shop2007/Camper_energy_saver/bluetooth_HC06/hc05-modulo.png

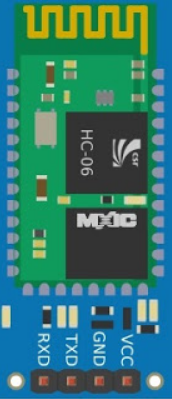
bluetooth_HC06/hc05-modulo.png
