shop2007/Camper_energy_saver/bluetooth_HC06/HC05.jpg

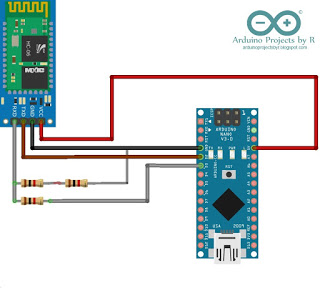
bluetooth_HC06/HC05.jpg
