shop2007/Camper_energy_saver/PDF-immagini/Apparato aperto.jpg

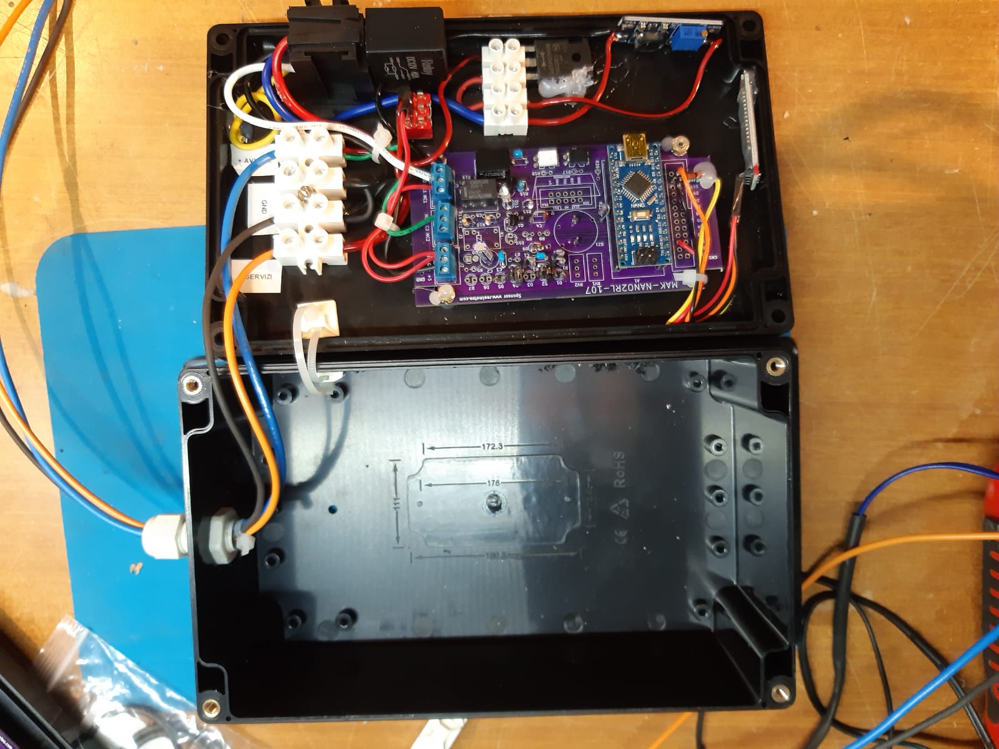
PDF-immagini/Apparato aperto.jpg
