shop2007/Camper_energy_saver/PDF-immagini/bluetooth terminal android 1a.jpg

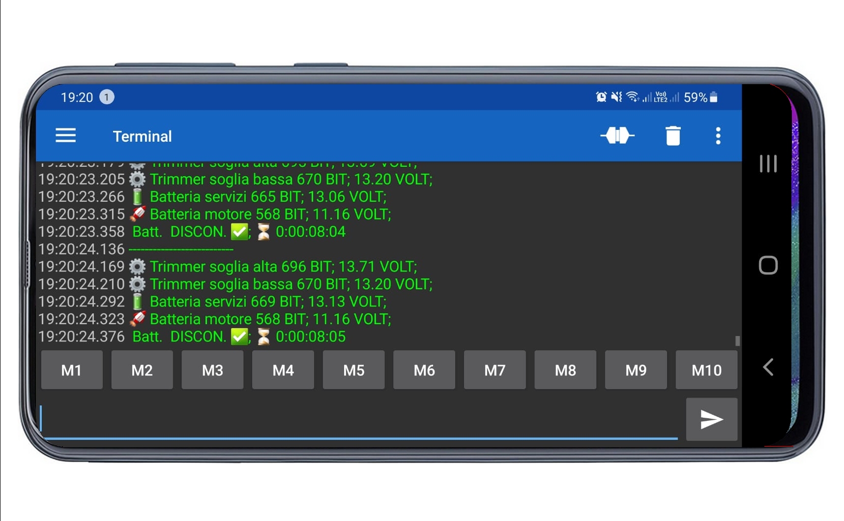
PDF-immagini/bluetooth terminal android 1a.jpg
