shop2007/Camper_energy_saver/PDF-immagini/bluetooth terminal android 2.jpg

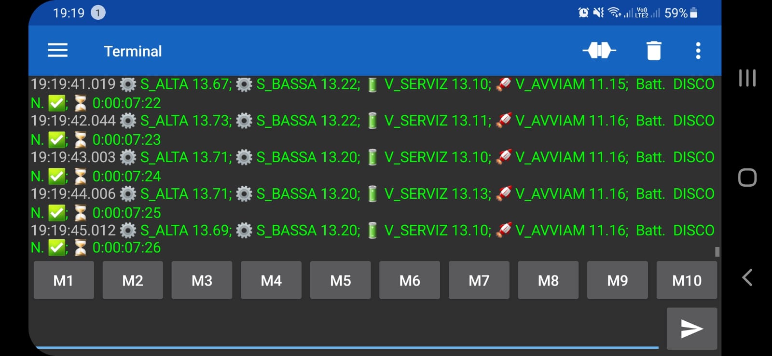
PDF-immagini/bluetooth terminal android 2.jpg
