shop2007/Camper_energy_saver/PDF-immagini/Cablaggio completo.jpg

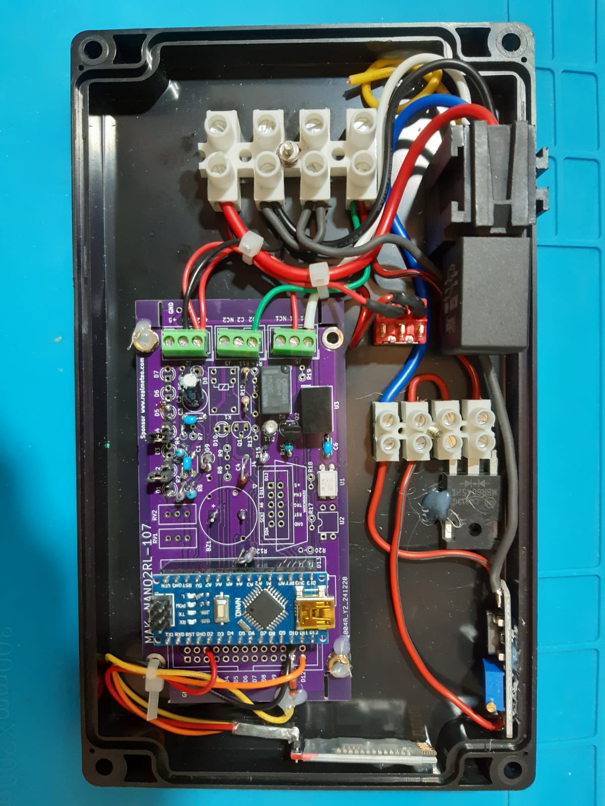
PDF-immagini/Cablaggio completo.jpg
