shop2007/Camper_energy_saver/PDF-immagini/CONNESSIONI.jpg

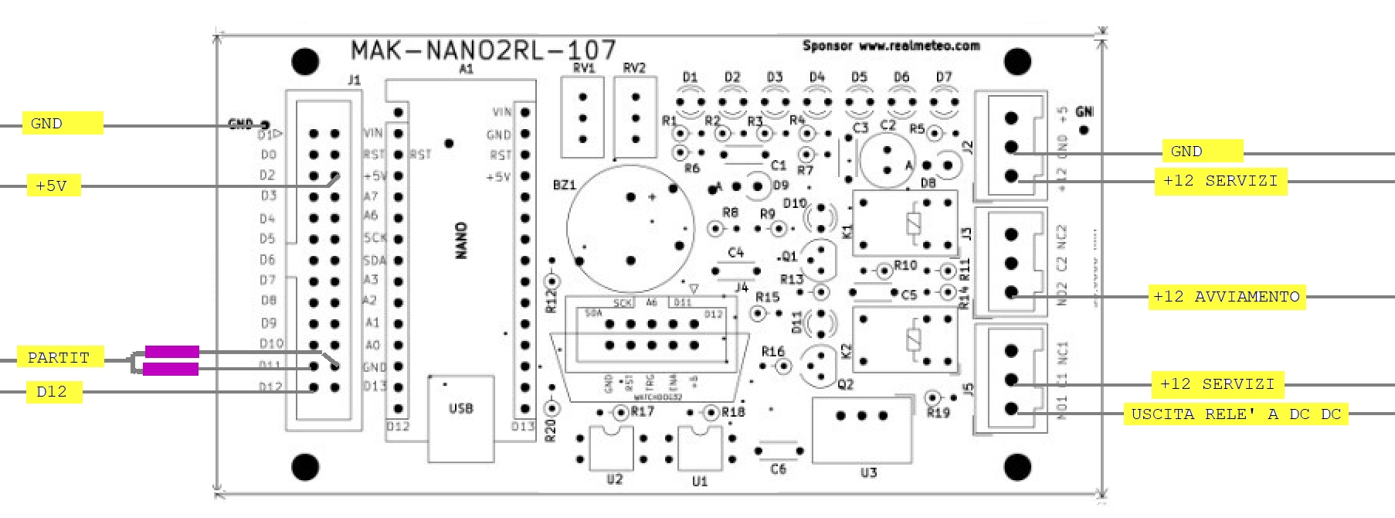
PDF-immagini/CONNESSIONI.jpg
