shop2007/Camper_energy_saver/PDF-immagini/Dettaglio arrivo batterie.jpg

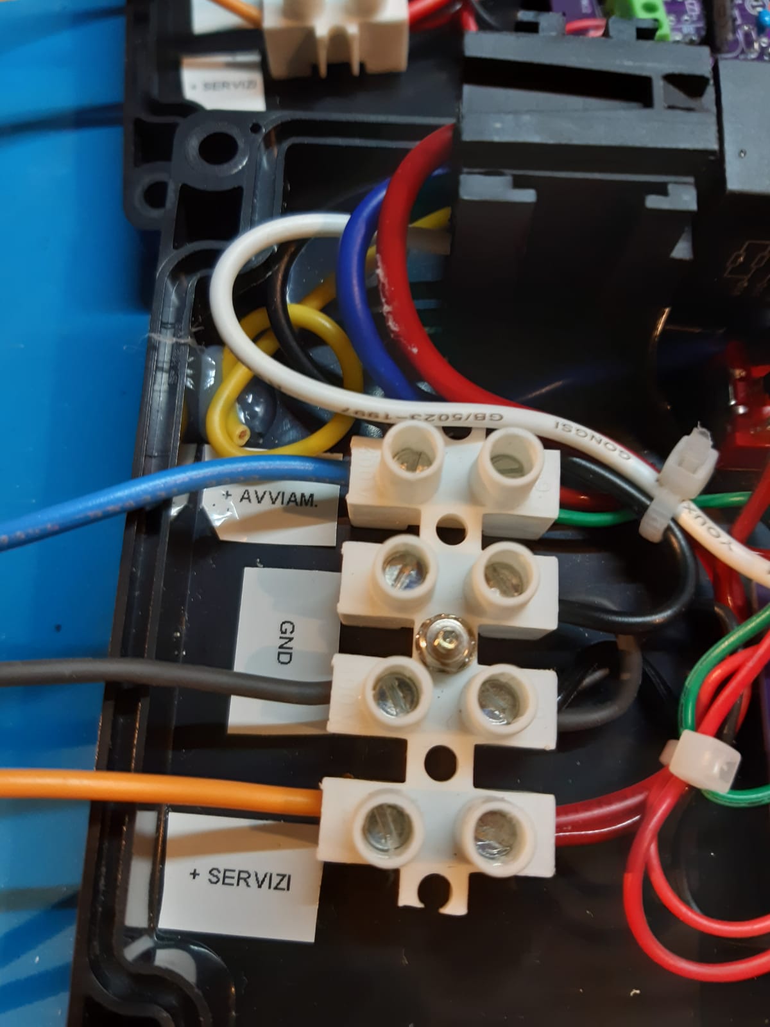
PDF-immagini/Dettaglio arrivo batterie.jpg
