shop2007/Camper_energy_saver/PDF-immagini/Dettaglio cablaggio.jpg

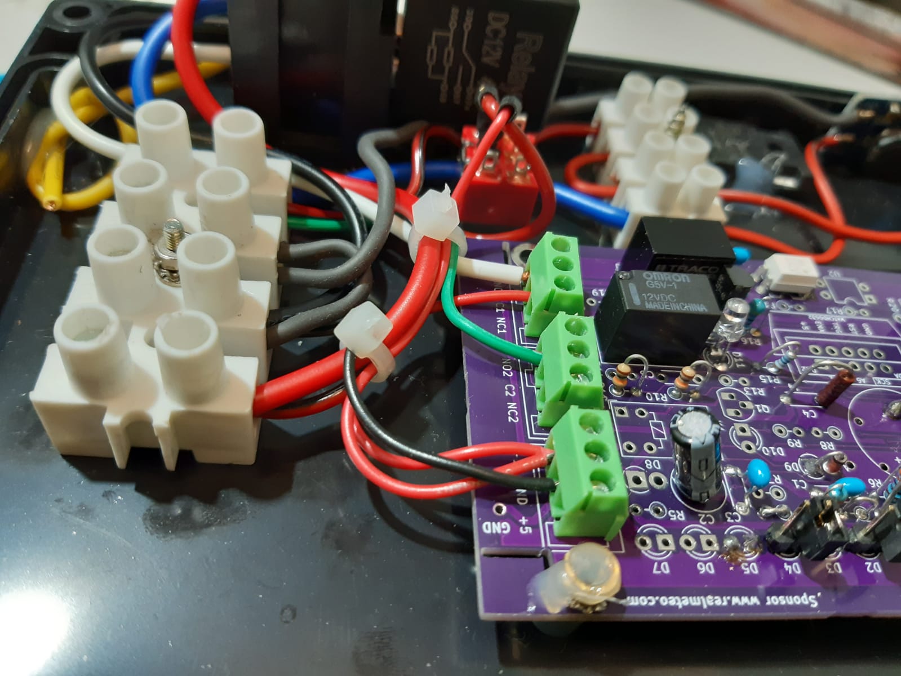
PDF-immagini/Dettaglio cablaggio.jpg
