shop2007/Camper_energy_saver/PDF-immagini/Dettaglio connessione modulo bluetooth.jpg

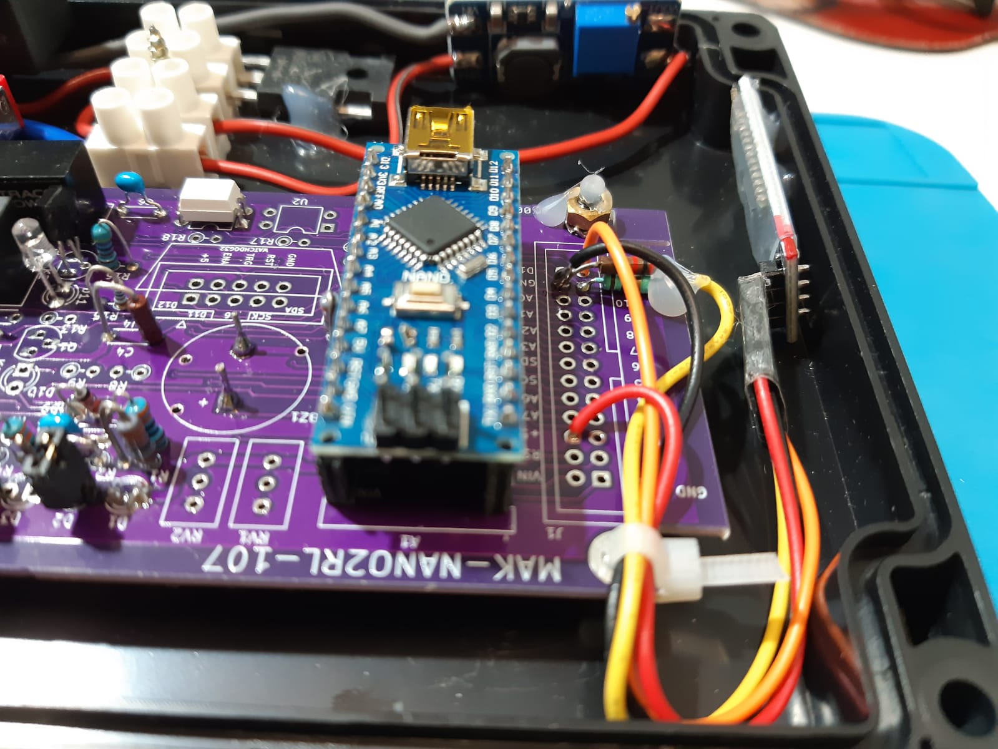
PDF-immagini/Dettaglio connessione modulo bluetooth.jpg
