shop2007/Camper_energy_saver/PDF-immagini/draft-impianto.jpg

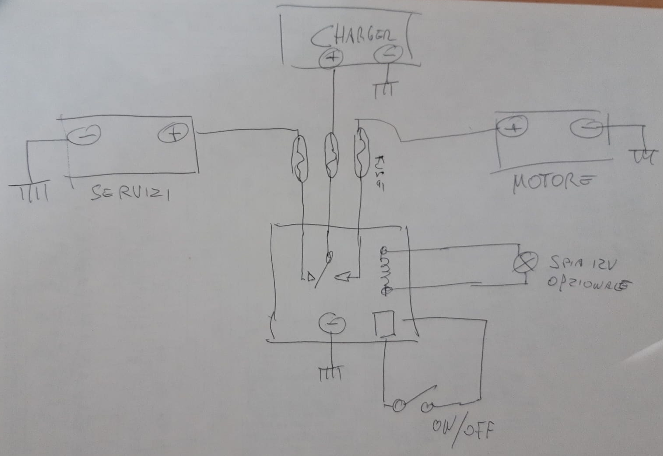
PDF-immagini/draft-impianto.jpg
