shop2007/Camper_energy_saver/PDF-immagini/Due prototipi 2.jpg

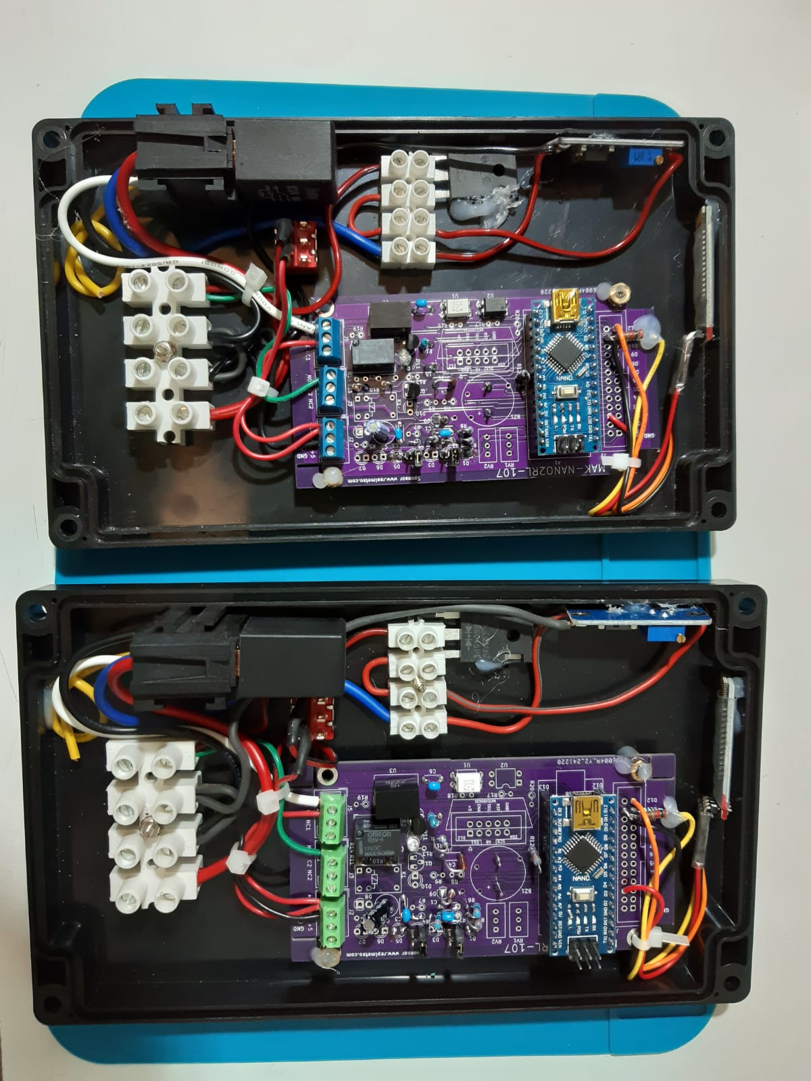
PDF-immagini/Due prototipi 2.jpg
