shop2007/Camper_energy_saver/PDF-immagini/Due prototipi gemelli.jpg

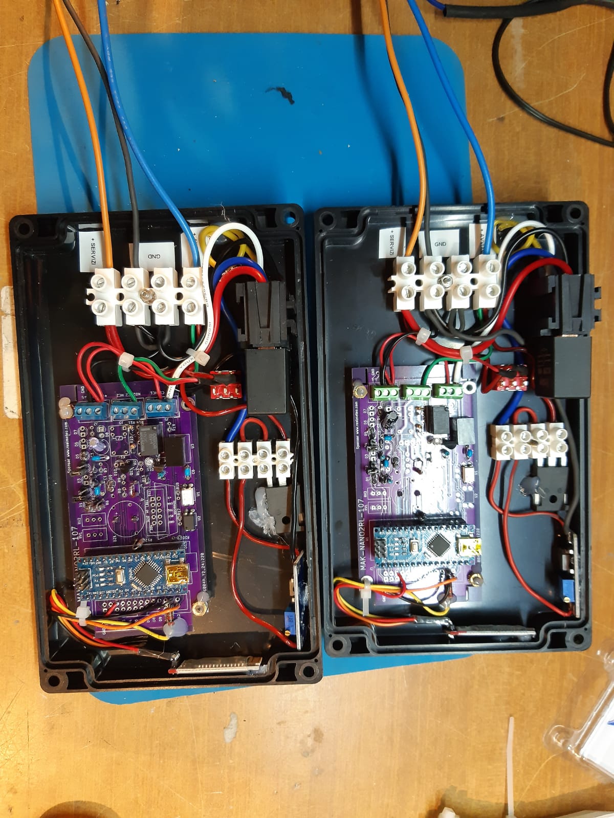
PDF-immagini/Due prototipi gemelli.jpg
