shop2007/Camper_energy_saver/PDF-immagini/led-jumper1.jpg

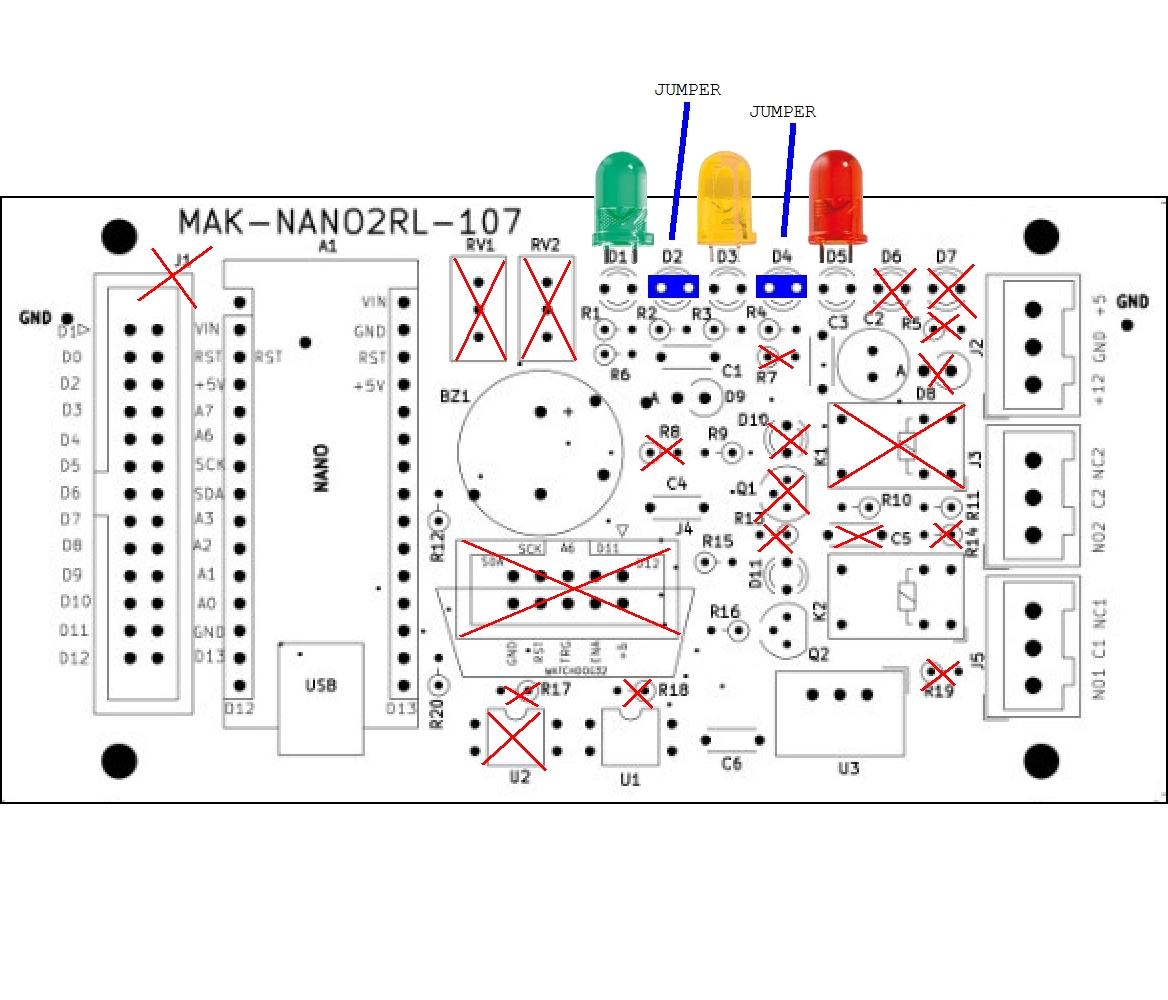
PDF-immagini/led-jumper1.jpg
