shop2007/Camper_energy_saver/PDF-immagini/mammut.png

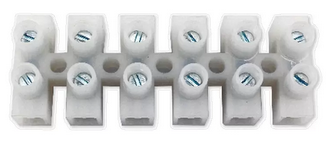
PDF-immagini/mammut.png
