shop2007/Camper_energy_saver/PDF-immagini/Modulo mak_nano2rl-107 montato.jpg

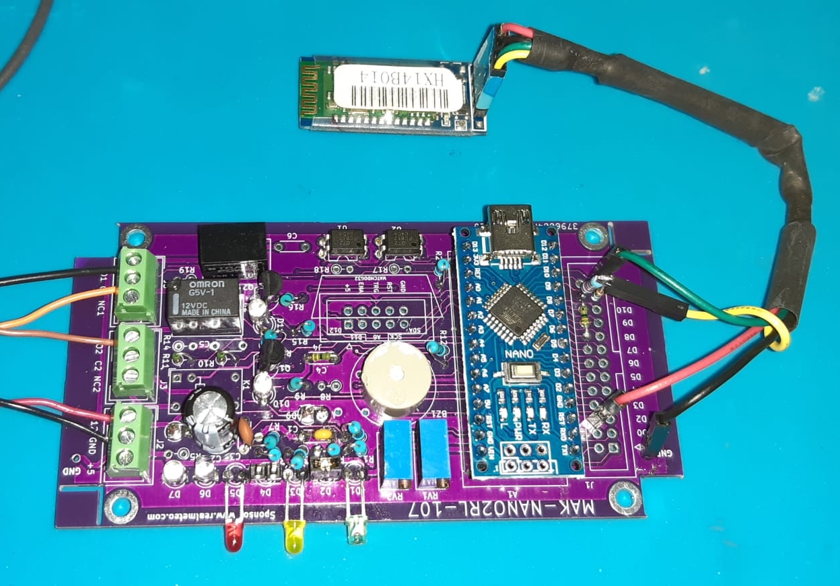
PDF-immagini/Modulo mak_nano2rl-107 montato.jpg
