shop2007/Camper_energy_saver/PDF-immagini/MORSETTIERA 4.jpg

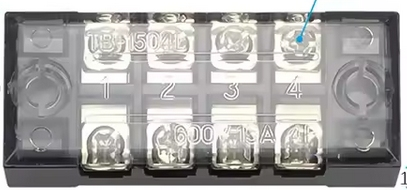
PDF-immagini/MORSETTIERA 4.jpg
