shop2007/Camper_energy_saver/PDF-immagini/PCB modulo-mak.jpg

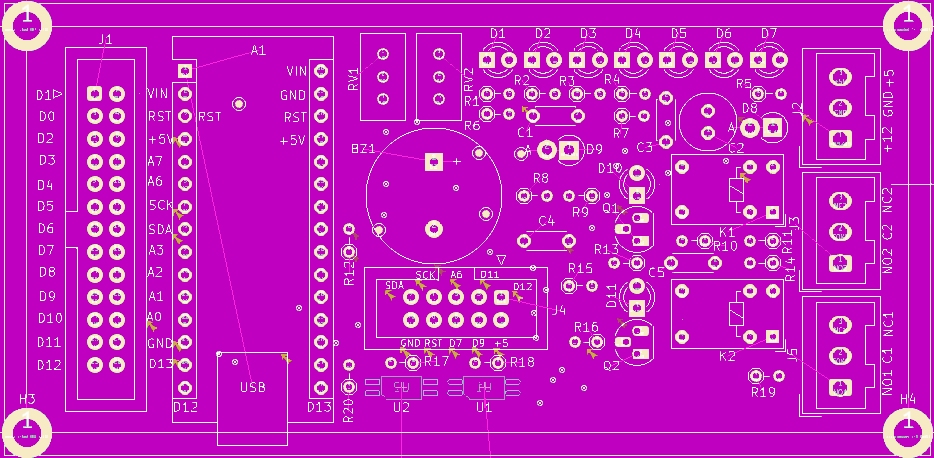
PDF-immagini/PCB modulo-mak.jpg
