shop2007/Camper_energy_saver/PDF-immagini/RELE 12V.jpg

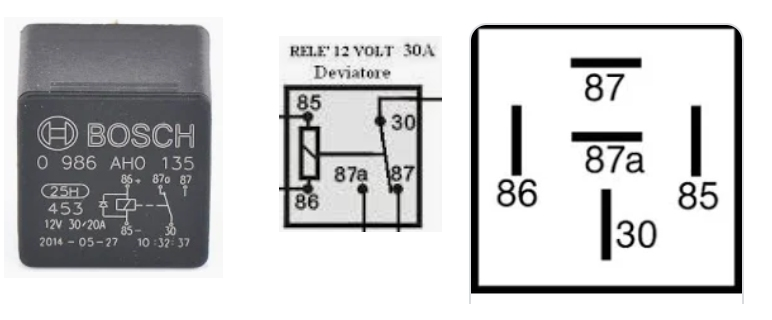
PDF-immagini/RELE 12V.jpg
