shop2007/Camper_energy_saver/PDF-immagini/rele auto mini2.png

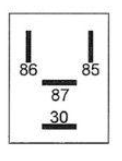
PDF-immagini/rele auto mini2.png
