shop2007/Camper_energy_saver/PDF-immagini/rele auto mini.png

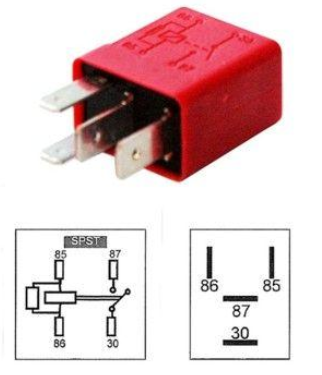
PDF-immagini/rele auto mini.png
