shop2007/Camper_energy_saver/PDF-immagini/RELE SLIM.jpg

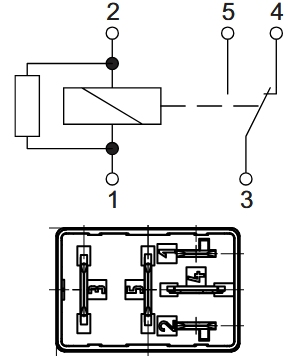
PDF-immagini/RELE SLIM.jpg
