shop2007/Camper_energy_saver/PDF-immagini/serial monitor 1.png

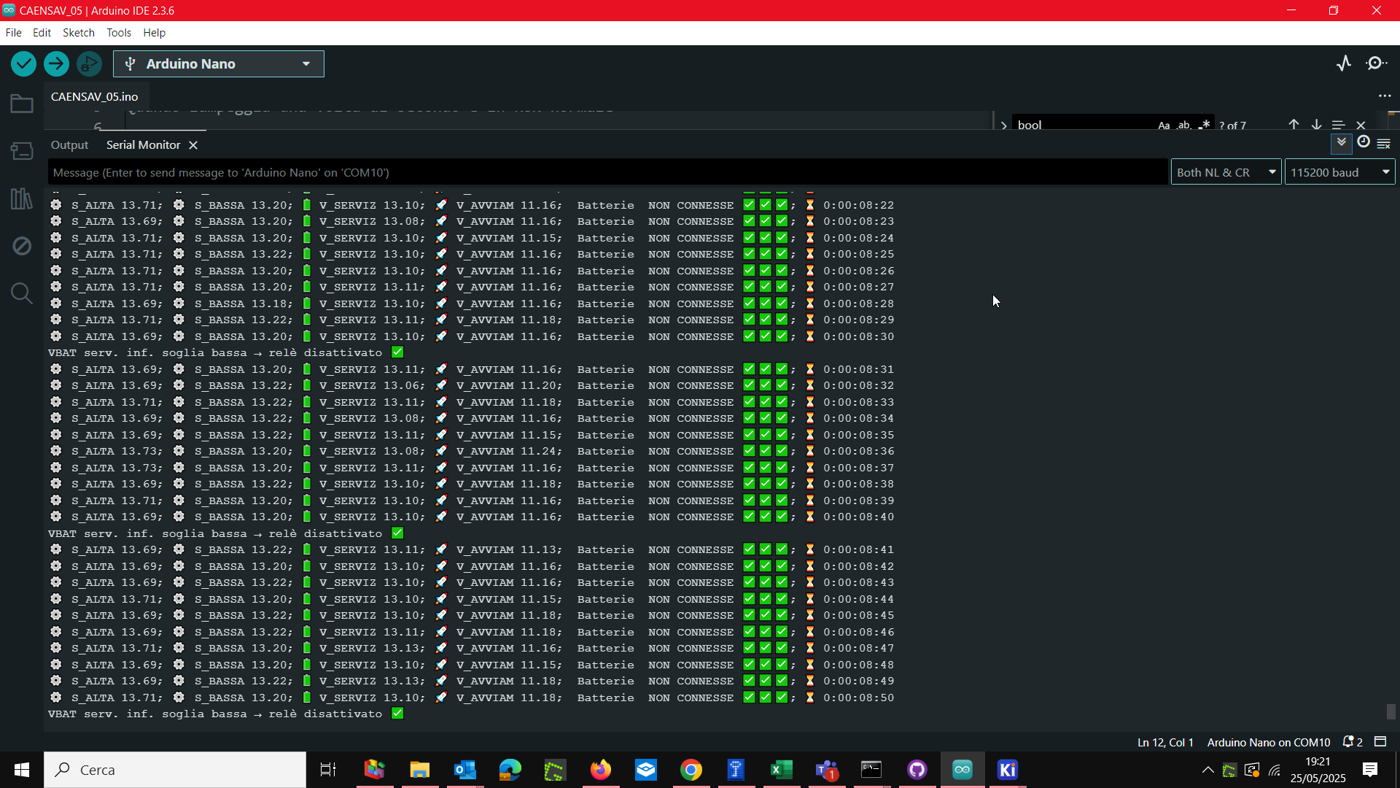
PDF-immagini/serial monitor 1.png
