shop2007/Camper_energy_saver/PDF-immagini/serial monitor 2.png

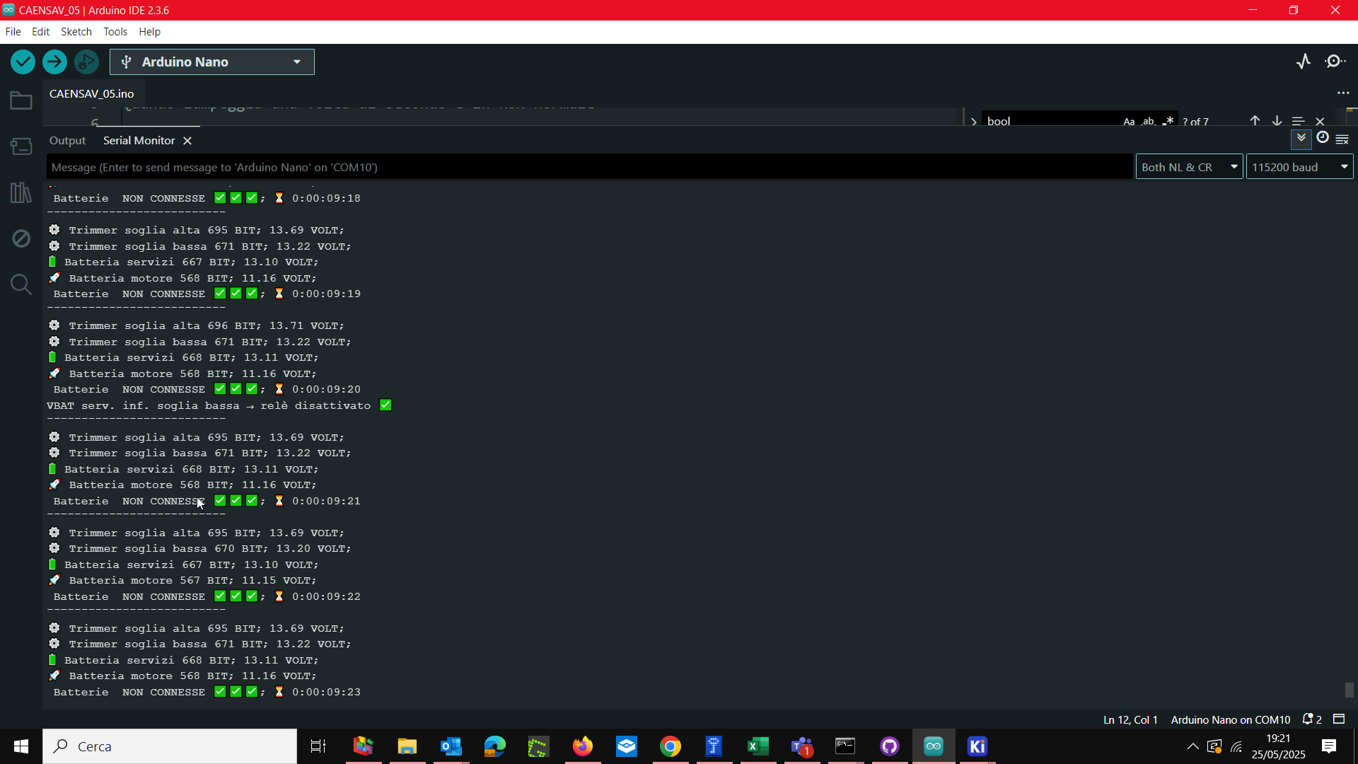
PDF-immagini/serial monitor 2.png
