shop2007/Camper_energy_saver/wiring schematic.jpg

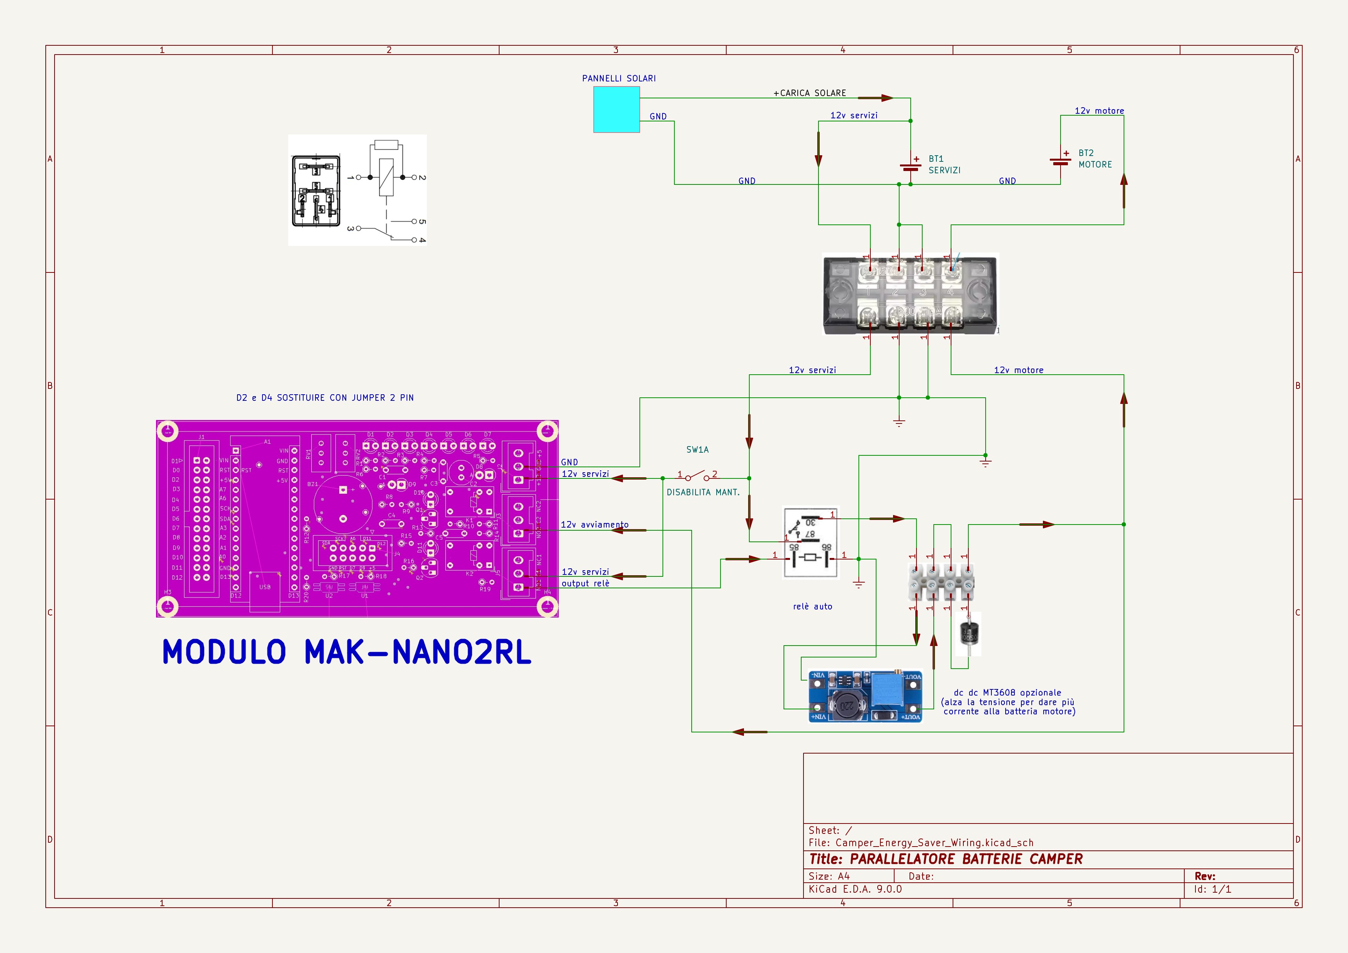
wiring schematic.jpg
