shop2007/Camper_energy_saver/Kicad/Camper_Energy_Saver_Wiring.kicad_sch

## KiCad design Kicad/Camper_Energy_Saver_Wiring.kicad_sch (2025-07-29)

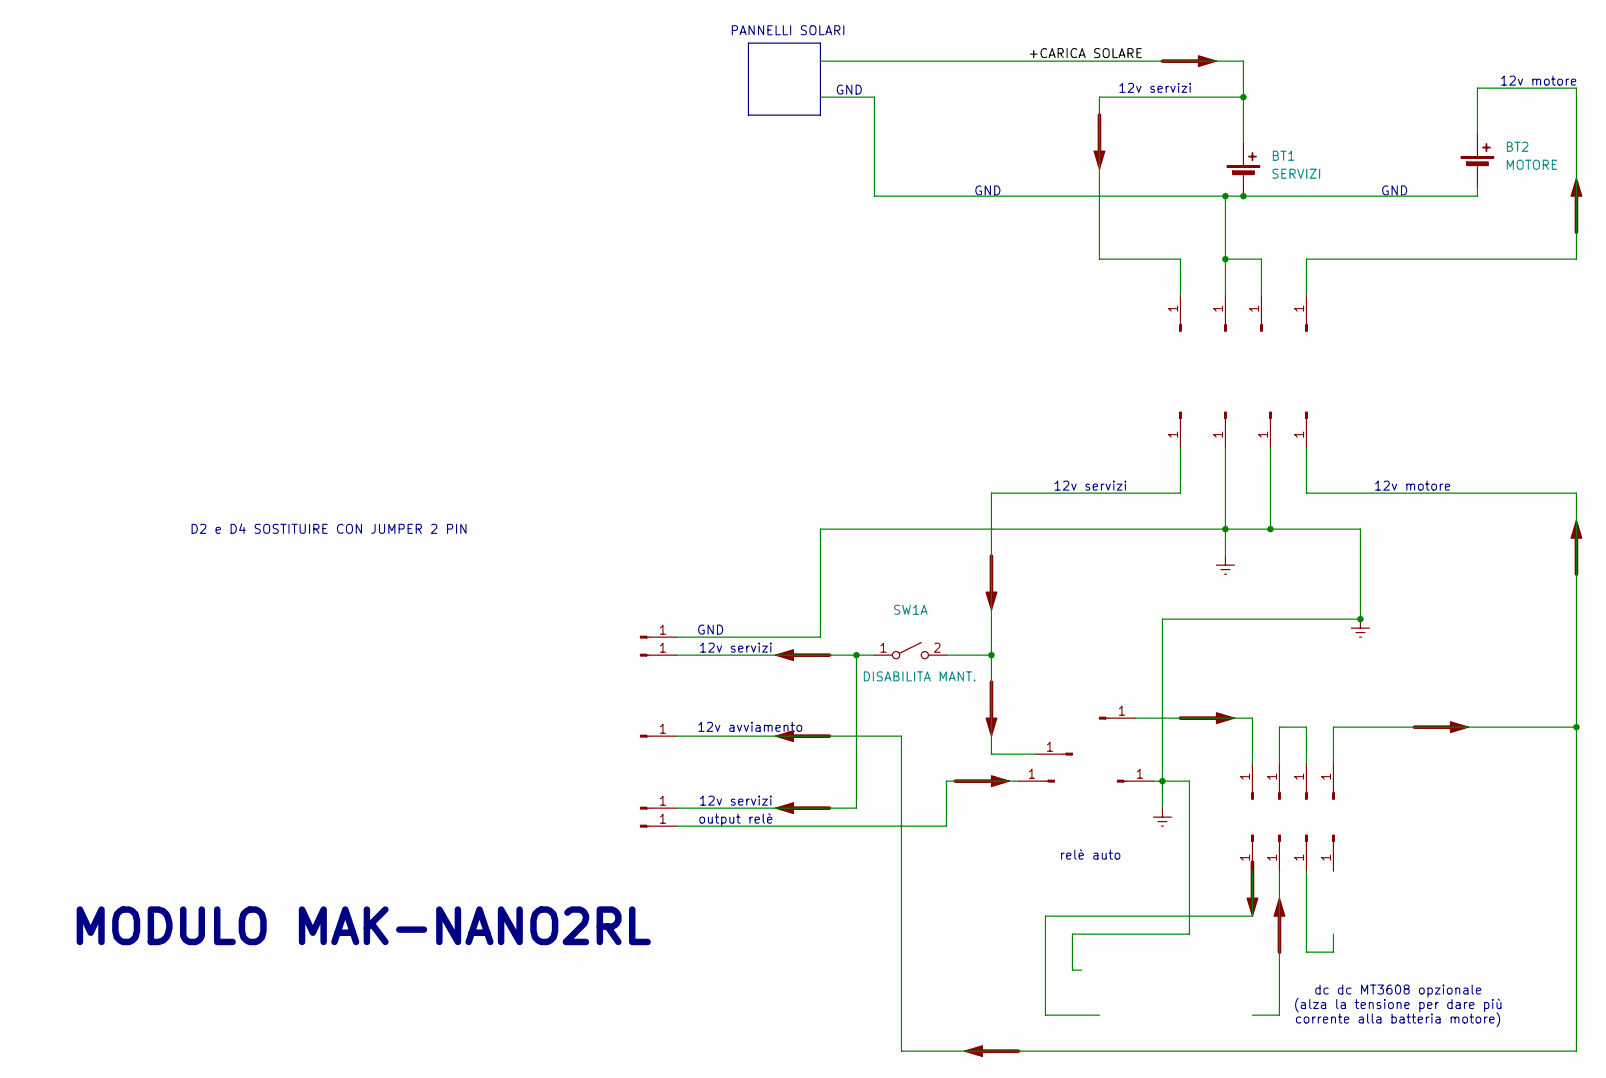
[picture p53: schematic Camper_Energy_Saver_Wiring.kicad_sch]

Parts:
BT1: SERVIZI
BT2: MOTORE
J10, J11, J12, J13, J14, J15, J16, J17, J18, J19, J20, J21, J22, J23, J24, J25, J26, J27, J28, J29, J30, J31, J32, J33, J34: Conn_01x01_Pin
SW1: DISABILITA MANT.

Connections:
+CARICA SOLARE: BT1.1 (+), J22.1
GNDREF: J12.1, J27.1, J28.1, J30.1
unnamed: BT1.2 (-), BT2.2 (-), J23.1, J24.1
unnamed: BT2.1 (+), J25.1
unnamed: J10.1, J34.1
unnamed: J11.1, J26.1, SW1.2 (B)
unnamed: J13.1, J14.1
unnamed: J15.1, J16.1
unnamed: J17.1, J29.1, J32.1
unnamed: J31.1, J33.1, SW1.1 (A)

Notes on the sheet:
12v motore
relè auto
GND
dc dc MT3608 opzionale (alza la tensione per dare più corrente alla batteria motore)
PANNELLI SOLARI
12v servizi
MODULO MAK-NANO2RL
12v avviamento
output relè
D2 e D4 SOSTITUIRE CON JUMPER 2 PIN
